SNURocketTeamHanaro/hanaro-daq/Data/180708-ancp-8mm/1.png

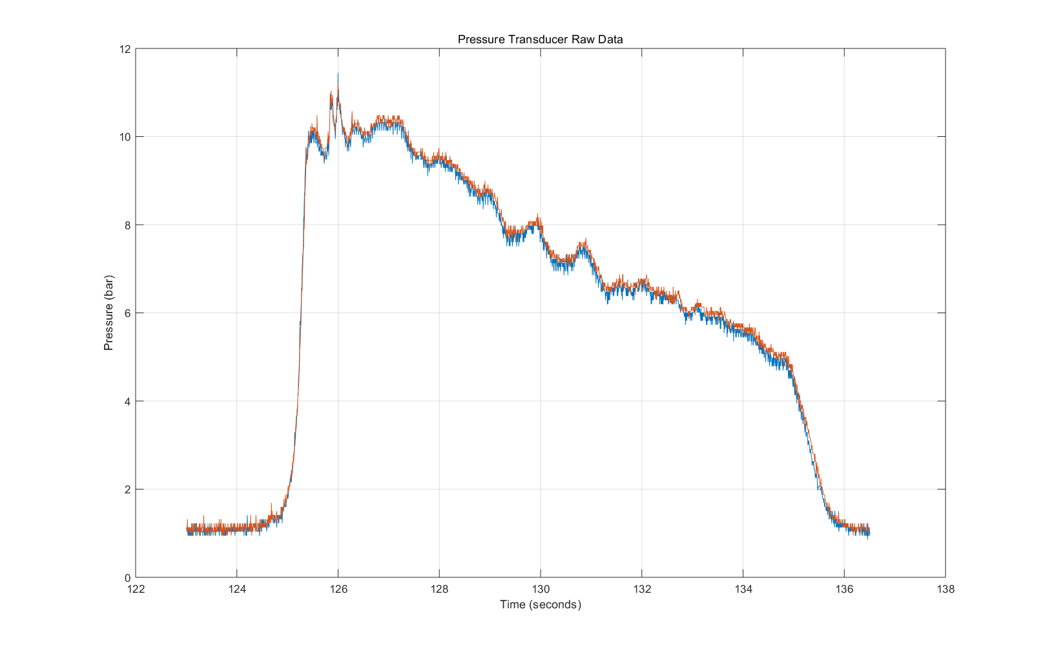
Data/180708-ancp-8mm/1.png
