SNURocketTeamHanaro/hanaro-daq/Data/180708-ancp-8mm/3.png

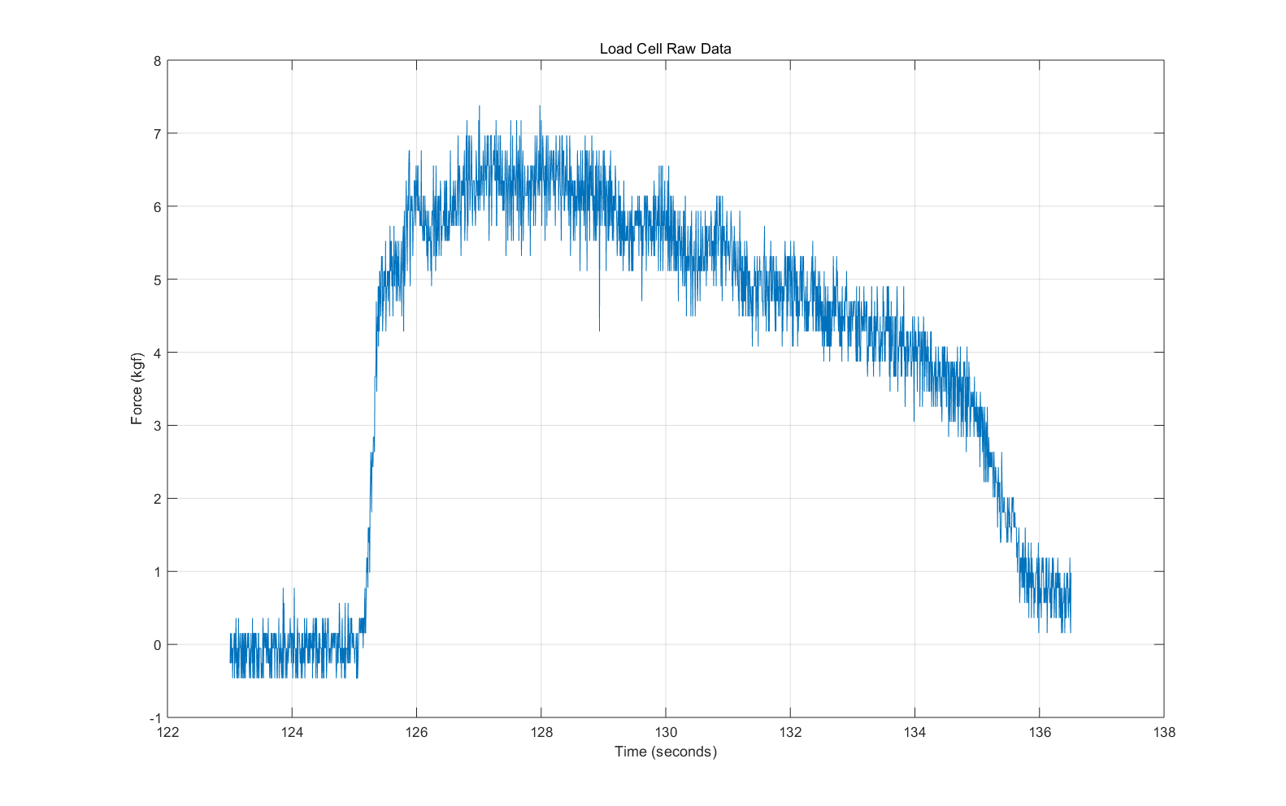
Data/180708-ancp-8mm/3.png
