SNURocketTeamHanaro/hanaro-daq/Data/180708-ancp-8mm/5.png

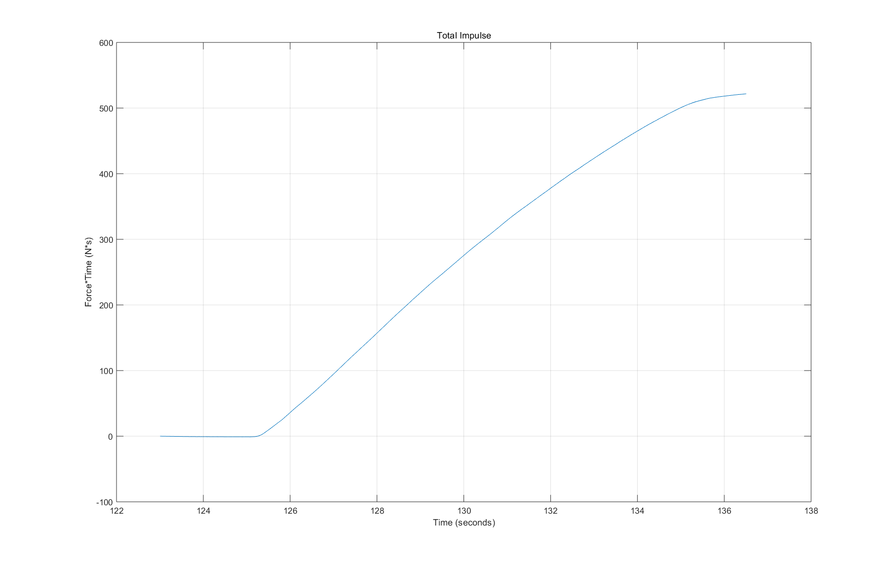
Data/180708-ancp-8mm/5.png
