SNURocketTeamHanaro/hanaro-daq/Data/180724-knsb-7mm/1.png

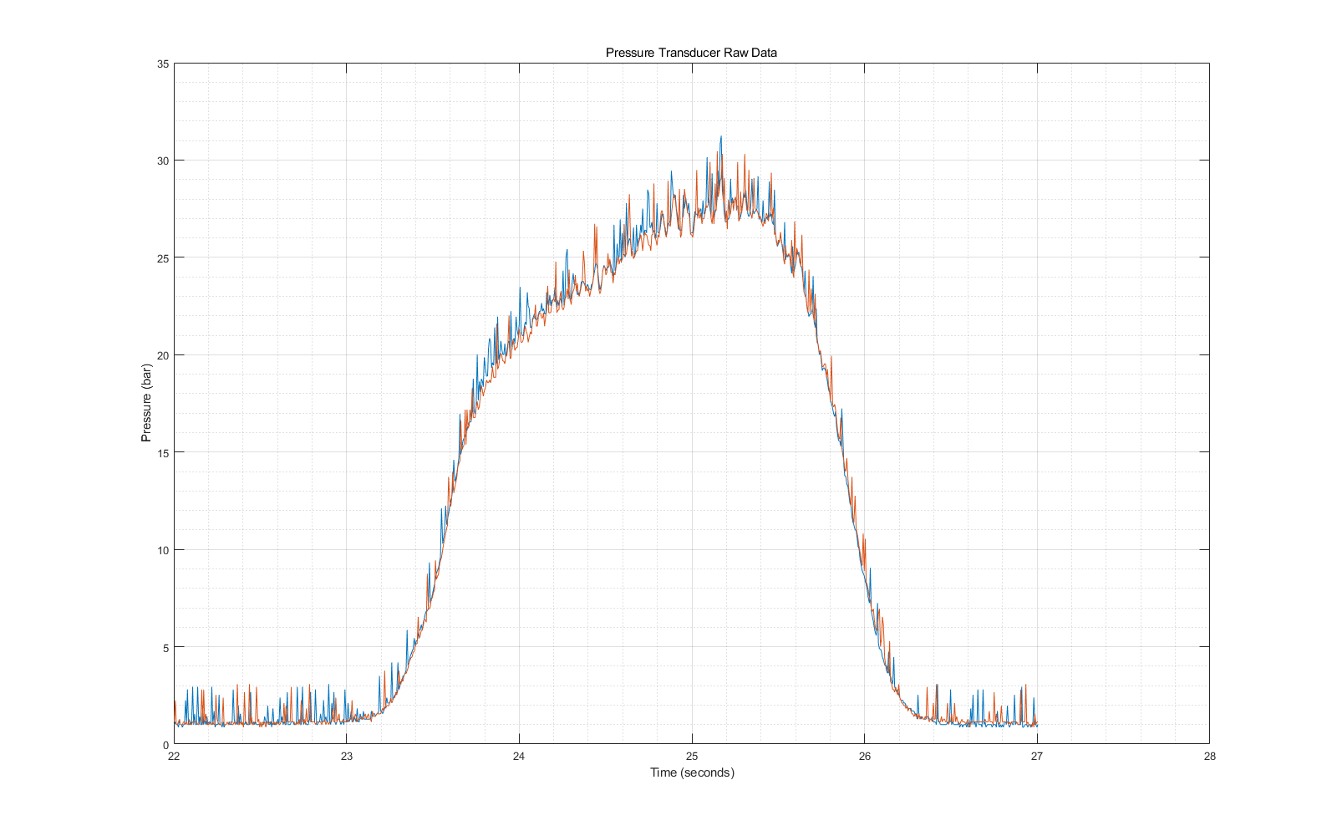
Data/180724-knsb-7mm/1.png
