SNURocketTeamHanaro/hanaro-daq/Data/180724-knsb-7mm/5.png

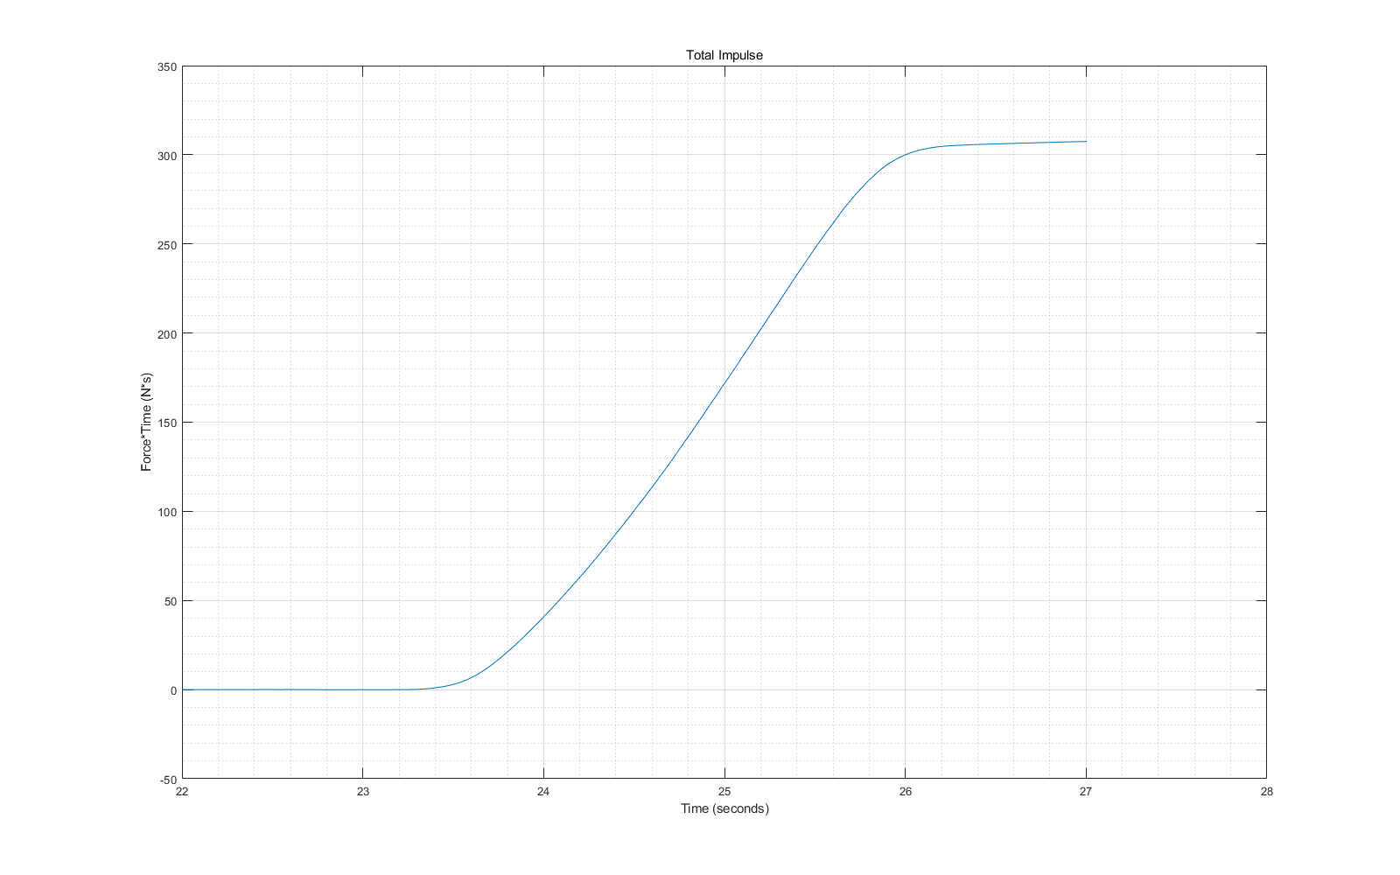
Data/180724-knsb-7mm/5.png
