SNURocketTeamHanaro/hanaro-daq/Data/180726-ancp-6mm/1.png

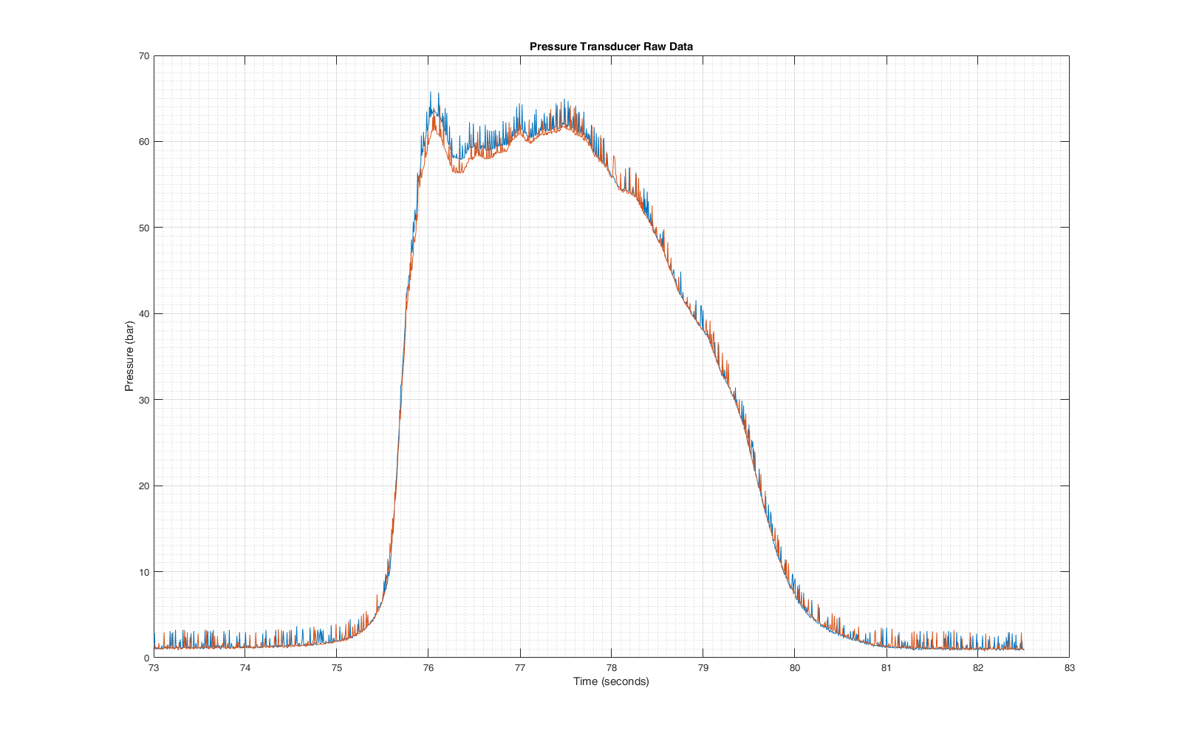
Data/180726-ancp-6mm/1.png
