SNURocketTeamHanaro/hanaro-daq/Data/180726-ancp-6mm/5.png

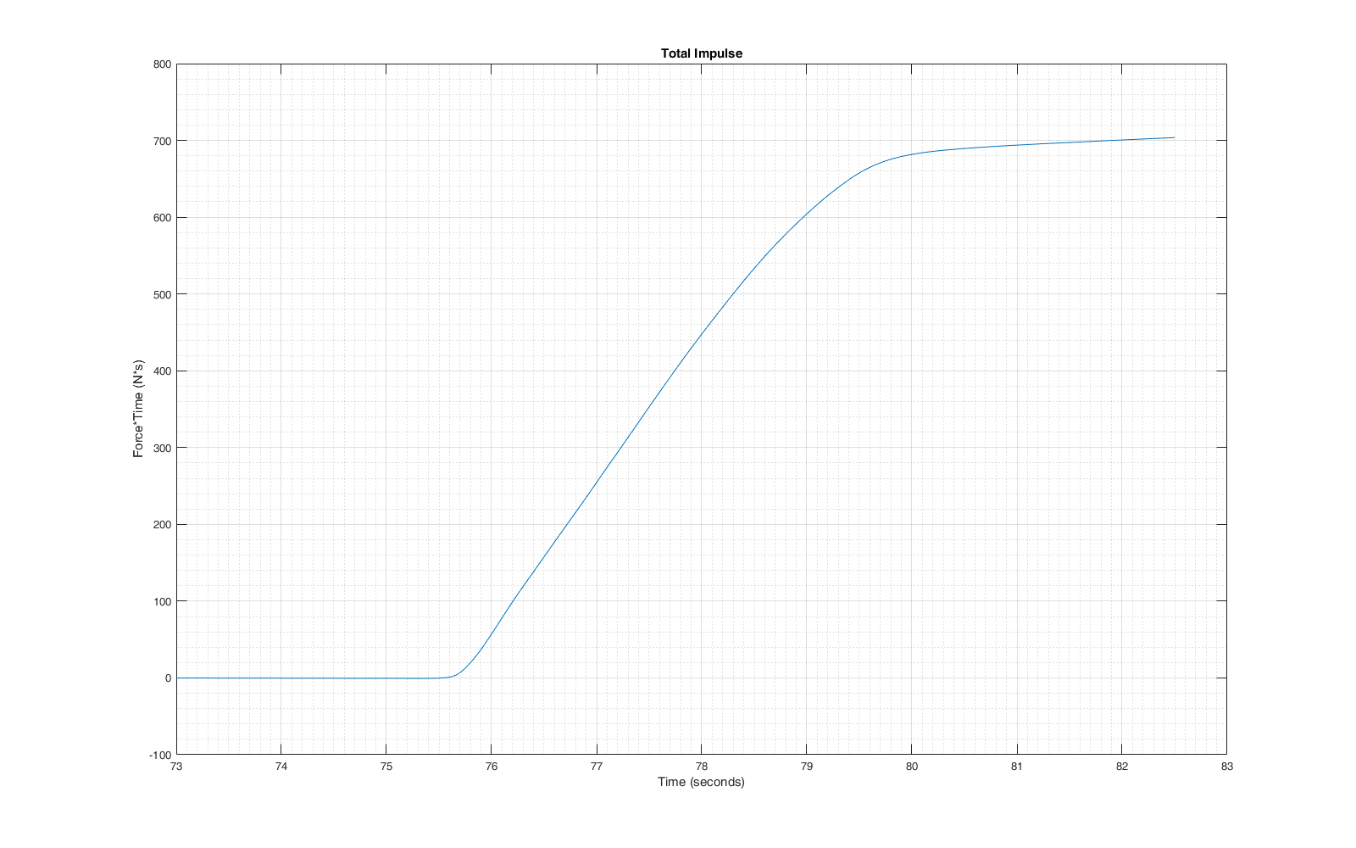
Data/180726-ancp-6mm/5.png
