SNURocketTeamHanaro/hanaro-daq/Data/180726-knsbyellow-7mm/1.png

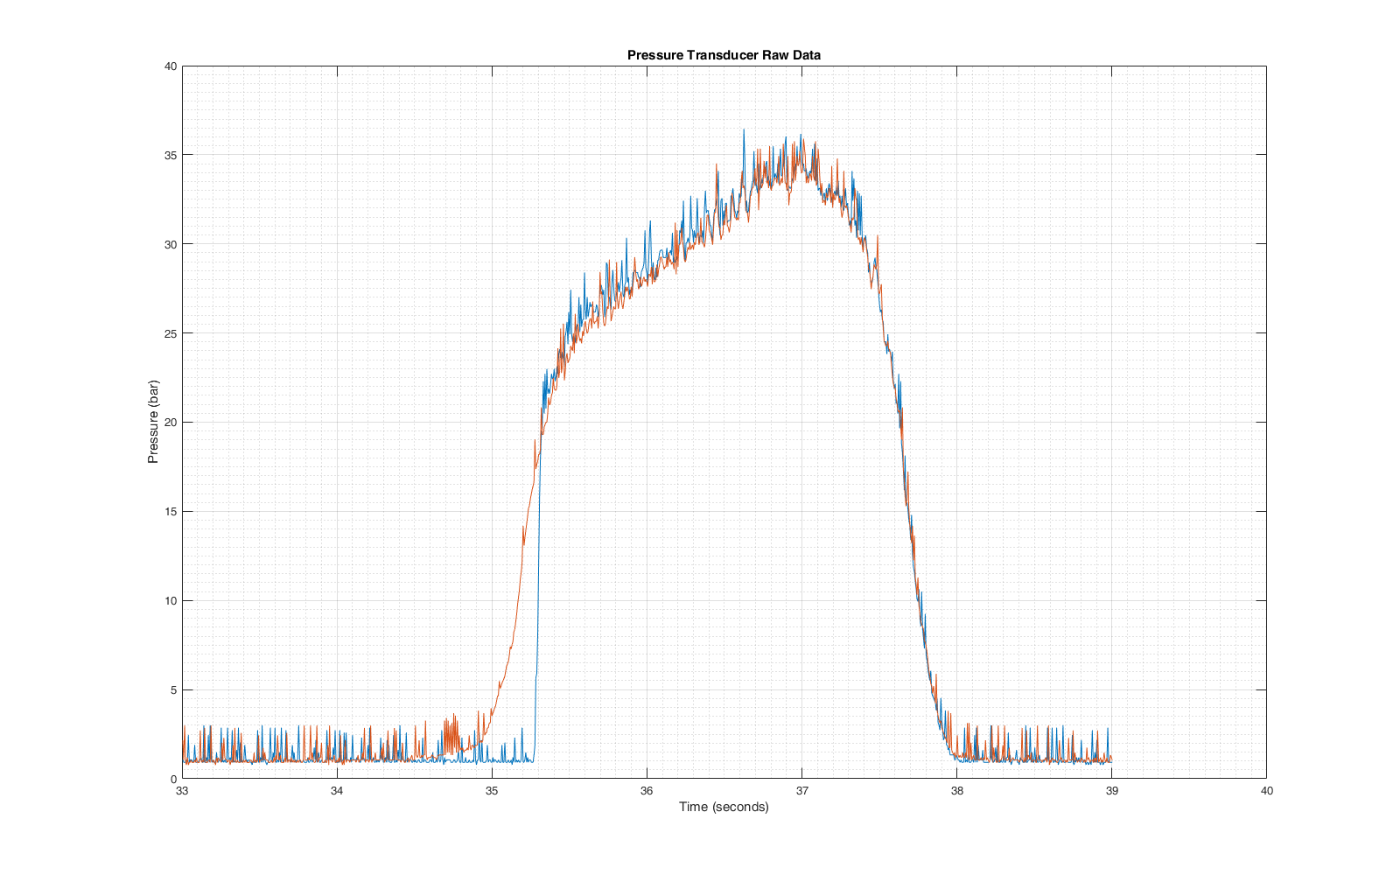
Data/180726-knsbyellow-7mm/1.png
