SNURocketTeamHanaro/hanaro-daq/Data/180726-knsbyellow-7mm/4.png

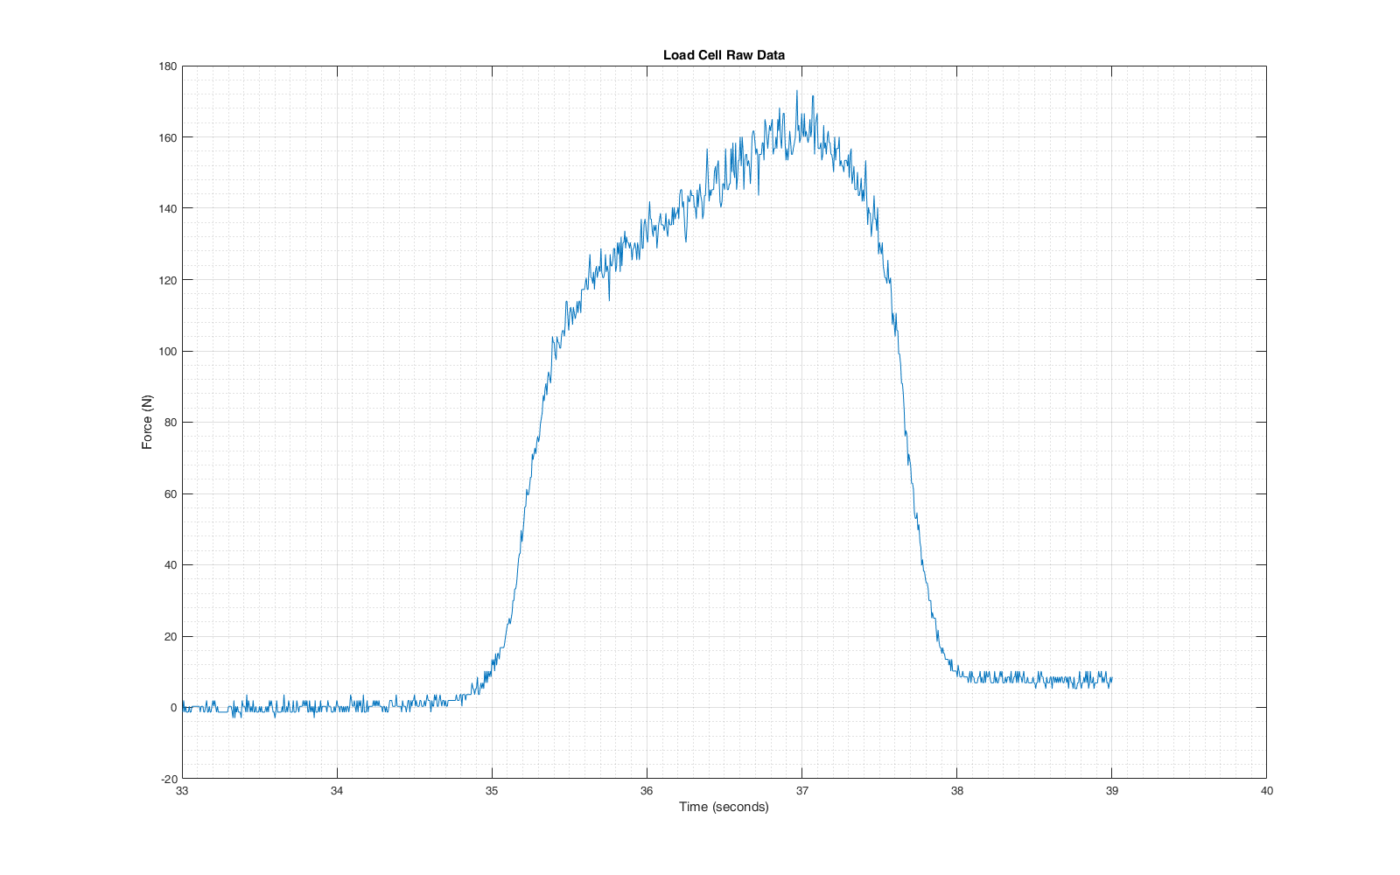
Data/180726-knsbyellow-7mm/4.png
