SNURocketTeamHanaro/hanaro-daq/Data/180724-knsb-7mm/BurnTest180724.xlsx

0 | 181 | 194 | 69 | 4.019049852 | 4.292096171 | 0 | 0.2876146919 | 1 | 2.797591824 | 336.9140625 | -0.04613680806 |  | pressure |  | ad620 offset | ad620 gain | loadcell multiplier
6 | 182 | 189 | 70 | 4.041254548 | 4.181475136 | 0.02220469532 | 0.1769936565 | 1.138779346 | 2.106210353 | 341.796875 | 0.1114972861 | resister | 219.9 | 220.7 | 338.3431784 | 400 | 0.6456692498
11 | 181 | 195 | 70 | 4.019049852 | 4.314220378 | 0 | 0.309738899 | 1 | 2.935868118 | 341.796875 | 0.1114972861 | offset | 4.019049852 | 4.004481479
17 | 181 | 194 | 69 | 4.019049852 | 4.292096171 | 0 | 0.2876146919 | 1 | 2.797591824 | 336.9140625 | -0.04613680806 | position | left | right | (bottom nozzle)
23 | 181 | 181 | 70 | 4.019049852 | 4.004481479 | 0 | 0 | 1 | 1 | 341.796875 | 0.1114972861
28 | 181 | 181 | 70 | 4.019049852 | 4.004481479 | 0 | 0 | 1 | 1 | 341.796875 | 0.1114972861
34 | 181 | 181 | 70 | 4.019049852 | 4.004481479 | 0 | 0 | 1 | 1 | 341.796875 | 0.1114972861
40 | 181 | 182 | 69 | 4.019049852 | 4.026605686 | 0 | 0.02212420707 | 1 | 1.138276294 | 336.9140625 | -0.04613680806
46 | 181 | 183 | 69 | 4.019049852 | 4.048729894 | 0 | 0.04424841414 | 1 | 1.276552588 | 336.9140625 | -0.04613680806
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
