SNURocketTeamHanaro/hanaro-daq/Data/180726-ancp-6mm/BurnTest180726-2.xlsx

0 | 189 | 192 | 80 | 4.196687415 | 4.247847757 | 0.002018608665 | 0.06637262121 | 1.012616304 | 1.414828883 | 390.625 | -0.1296515473 |  | pressure |  | ad620 offset | ad620 gain | loadcell multiplier
6 | 189 | 189 | 81 | 4.196687415 | 4.181475136 | 0.002018608665 | 0 | 1.012616304 | 1 | 395.5078125 | 0.03823992266 | resister | 219.9 | 220.7 | 394.3956752 | 400 | 0.687683461
11 | 189 | 188 | 81 | 4.196687415 | 4.159350929 | 0.002018608665 | -0.02212420707 | 1.012616304 | 0.8617237058 | 395.5078125 | 0.03823992266 | offset | 4.194668806 | 4.181475136 |  |  | 0.6456692498
17 | 188 | 188 | 82 | 4.174482719 | 4.159350929 | -0.02018608665 | -0.02212420707 | 0.8738369584 | 0.8617237058 | 400.390625 | 0.2061313926 | position | left | right | (bottom nozzle)
23 | 192 | 189 | 80 | 4.263301501 | 4.181475136 | 0.06863269461 | 0 | 1.428954341 | 1 | 390.625 | -0.1296515473
28 | 190 | 189 | 80 | 4.21889211 | 4.181475136 | 0.02422330398 | 0 | 1.15139565 | 1 | 390.625 | -0.1296515473
34 | 190 | 189 | 81 | 4.21889211 | 4.181475136 | 0.02422330398 | 0 | 1.15139565 | 1 | 395.5078125 | 0.03823992266
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
