SNURocketTeamHanaro/hanaro-daq/Data/180726-knsbyellow-7mm/BurnTest180726-1.xlsx

0 | 186 | 186 | 80 | 4.130073329 | 4.115102515 | -0.01268839732 | -0.01382762942 | 0.9206975167 | 0.9135773161 | 390.625 | 0.03275931121 |  | pressure |  | ad620 offset | ad620 gain | loadcell multiplier
6 | 187 | 187 | 80 | 4.152278024 | 4.137226722 | 0.009516297993 | 0.008296577651 | 1.059476862 | 1.05185361 | 390.625 | 0.03275931121 | resister | 219.9 | 220.7 | 389.6722561 | 400 | 0.687683461
11 | 186 | 186 | 79 | 4.130073329 | 4.115102515 | -0.01268839732 | -0.01382762942 | 0.9206975167 | 0.9135773161 | 385.7421875 | -0.1351321588 | offset | 4.142761726 | 4.128930144 |  |  | 0.6456692498
17 | 186 | 186 | 80 | 4.130073329 | 4.115102515 | -0.01268839732 | -0.01382762942 | 0.9206975167 | 0.9135773161 | 390.625 | 0.03275931121 | position | left | right | (bottom nozzle)
23 | 186 | 187 | 79 | 4.130073329 | 4.137226722 | -0.01268839732 | 0.008296577651 | 0.9206975167 | 1.05185361 | 385.7421875 | -0.1351321588
28 | 187 | 188 | 79 | 4.152278024 | 4.159350929 | 0.009516297993 | 0.03042078472 | 1.059476862 | 1.190129904 | 385.7421875 | -0.1351321588
34 | 187 | 186 | 80 | 4.152278024 | 4.115102515 | 0.009516297993 | -0.01382762942 | 1.059476862 | 0.9135773161 | 390.625 | 0.03275931121
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
